openenergymonitor/emontx3/enclosure/fascia/fascia.png

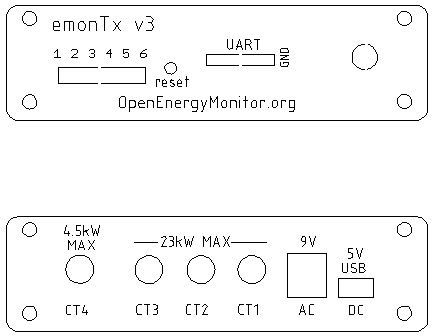
enclosure/fascia/fascia.png
