openenergymonitor/emontx3/testing/ds18b20-test/src/src.ino

#include <OneWire.h>
#include <DallasTemperature.h>

// Data wire is plugged into port 2 on the Arduino
#define ONE_WIRE_BUS 5
#define TEMPERATURE_PRECISION 9 // Lower resolution
const byte DS18B20_PWR=            19;
const byte LEDpin=                 6;


// Setup a oneWire instance to communicate with any OneWire devices (not just Maxim/Dallas temperature ICs)
OneWire oneWire(ONE_WIRE_BUS);

// Pass our oneWire reference to Dallas Temperature.
DallasTemperature sensors(&oneWire);

int numberOfDevices; // Number of temperature devices found

DeviceAddress tempDeviceAddress; // We'll use this variable to store a found device address

void setup(void)
{
  // start serial port
  Serial.begin(115200);
  Serial.println("DS18B20 emonTx Tester");

  pinMode(LEDpin, OUTPUT);
  pinMode(DS18B20_PWR, OUTPUT);
  digitalWrite(DS18B20_PWR, HIGH);
  digitalWrite(LEDpin, HIGH); delay(100); digitalWrite(LEDpin, LOW);

  // Start up the library
  sensors.begin();
  delay(1000);  //added to give the onewire stuff time to initialize.
  sensors.requestTemperatures();

  // Grab a count of devices on the wire
  numberOfDevices = sensors.getDeviceCount();

  // locate devices on the bus
  //Serial.print("Locating devices...");

  //Serial.print("Found ");
  //Serial.print(numberOfDevices, DEC);
  //Serial.println(" devices.");

  // report parasite power requirements
  //Serial.print("Parasite power is: ");
  //if (sensors.isParasitePowerMode()) Serial.println("ON");
  //else Serial.println("OFF");

  // Loop through each device, print out address
  for(int i=0;i<numberOfDevices; i++)
  {
    // Search the wire for address
    if(sensors.getAddress(tempDeviceAddress, i))
	{

		//Serial.print("Found device ");
		//Serial.print(i, DEC);
		//Serial.print(" with address: ");
		//printAddress(tempDeviceAddress);
		//Serial.println();

		//Serial.print("Setting resolution to ");
		//Serial.println(TEMPERATURE_PRECISION, DEC);

		// set the resolution to TEMPERATURE_PRECISION bit (Each Dallas/Maxim device is capable of several different resolutions)
		sensors.setResolution(tempDeviceAddress, TEMPERATURE_PRECISION);

		//Serial.print("Resolution actually set to: ");
		//Serial.print(sensors.getResolution(tempDeviceAddress), DEC);
		//Serial.println();
    sensors.requestTemperatures();
    delay(1000);  //some DS19B20 can take 750ms to perform temp conversion. Fix for 2021 batch of RJ45 temp sensors 
    Serial.print("Temperature: ");
    float tempC = sensors.getTempC(tempDeviceAddress);
    if ((tempC<80.0) && (tempC>-10.0)){
      Serial.print(tempC);
      Serial.println();
      digitalWrite(LEDpin, HIGH);
    } else {
      Serial.print("ERROR temperature out of limit ");
      Serial.print(tempC);
      digitalWrite(LEDpin, LOW);
    }
    //printTemperature(tempDeviceAddress); // Use a simple function to print out the data

	}else{
		Serial.print("Found ghost device at ");
		Serial.print(i, DEC);
		Serial.print(" but could not detect address. Check power and cabling");
    digitalWrite(LEDpin, LOW);
	}
  }

}

// function to print the temperature for a device
void printTemperature(DeviceAddress deviceAddress)
{
  // method 1 - slower
  //Serial.print("Temp C: ");
  //Serial.print(sensors.getTempC(deviceAddress));
  //Serial.print(" Temp F: ");
  //Serial.print(sensors.getTempF(deviceAddress)); // Makes a second call to getTempC and then converts to Fahrenheit

  // method 2 - faster
  float tempC = sensors.getTempC(deviceAddress);
  Serial.print("Temp C: ");
  Serial.print(tempC);
  Serial.print(" Temp F: ");
  Serial.println(DallasTemperature::toFahrenheit(tempC)); // Converts tempC to Fahrenheit
}

void loop()
{

 // while(1){

  //}
  // // call sensors.requestTemperatures() to issue a global temperature
  // // request to all devices on the bus
  // Serial.print("Requesting temperatures...");
  // sensors.requestTemperatures(); // Send the command to get temperatures
  // Serial.println("DONE");
  //
  //
  // // Loop through each device, print out temperature data
  // for(int i=0;i<numberOfDevices; i++)
  // {
  //   // Search the wire for address
  //   if(sensors.getAddress(tempDeviceAddress, i))
	// {
	// 	// Output the device ID
	// 	Serial.print("Temperature for device: ");
	// 	Serial.println(i,DEC);
  //
	// 	// It responds almost immediately. Let's print out the data
	// 	printTemperature(tempDeviceAddress); // Use a simple function to print out the data
	// }
	// //else ghost device! Check your power requirements and cabling
  //
  // }


      delay(1000);  //some DS19B20 can take 750ms to perform temp conversion. Fix for 2021 batch of RJ45 temp sensors
    Serial.print("Temperature: ");
    float tempC = sensors.getTempC(tempDeviceAddress);
    if ((tempC<80.0) && (tempC>-10.0)){
      Serial.print(tempC);
      Serial.println();
      digitalWrite(LEDpin, HIGH);
    } else {
      Serial.print("ERROR temperature out of limit ");
      Serial.print(tempC);
      digitalWrite(LEDpin, LOW);
    }

}

// function to print a device address
void printAddress(DeviceAddress deviceAddress)
{
  for (uint8_t i = 0; i < 8; i++)
  {
    if (deviceAddress[i] < 16) Serial.print("0");
    Serial.print(deviceAddress[i], HEX);
  }
}
